ikatkov/mains-psu-15V/ltspice/psu.asc

B1: bv; V=(white(2e6*time/10000))/100
C1: cap; {Cin}
C2: cap; {Cin}
C3: cap; {Cin2}
C4: cap; {Cin2}
C5: cap; 100n
C6: cap; 100n
C7: cap; 100n
C8: cap; 100n
C9: cap; {Cout}
C10: cap; {Cout}
D1: diode
D2: diode
D5: diode
D6: diode
D7: zener; BZX84C15L
D8: diode
D9: diode
E1: e; 1
R1: res; 3
R2: res; 3
R3: res; 84
R4: res; 84
R5: res; 1m
R6: res; 1m
U1: regulators
U2: regulators
V1: voltage; SINE(0 25 60)
Named nets: 0, NOISE
.tran 200ms
.param Cin=470u Cin2=1000u
.param Cout=10u
2A fuse
